eejai42/med-reminder/CarrierBox/box_v7_no_lid.stl

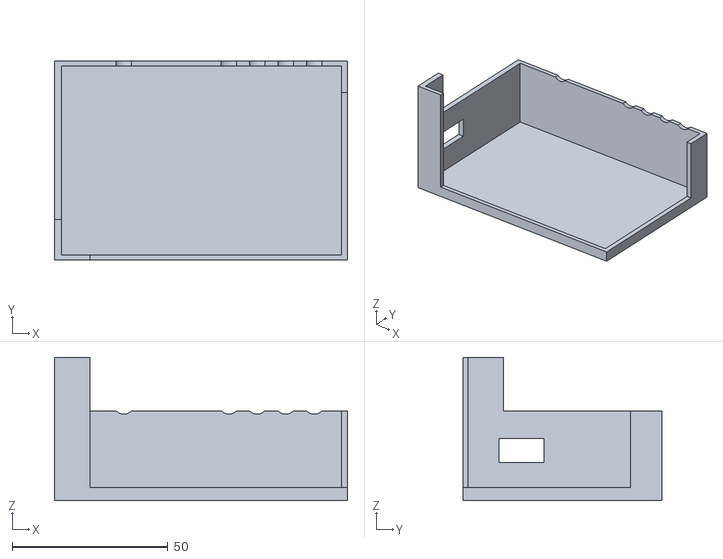
[picture p19: CAD file, 2024-03-23, an earlier design]
CarrierBox/box_v7_no_lid.stl
94.0 x 64.0 x 46.0
