eejai42/med-reminder/PillBoxInserts/InsertTestSlice_v2_1pc.stl

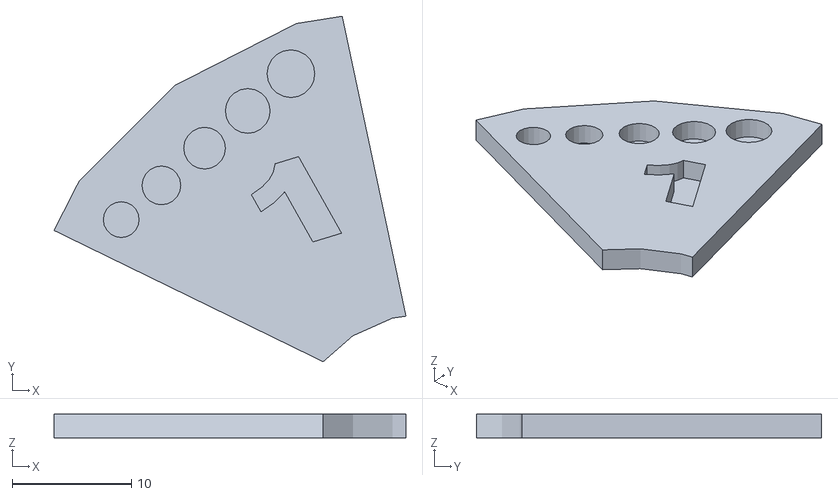
[picture p20: CAD file, 2024-03-27, an earlier design]
PillBoxInserts/InsertTestSlice_v2_1pc.stl
29.6 x 29.0 x 2.00
