eejai42/med-reminder/arduino2/Alerting.cpp

#pragma once
#include "MedReminderStateMachine.h"

bool MedReminderStateMachine::hasAlerting_MovementDetected() {
  return true;
}

void MedReminderStateMachine::enterAlerting(State currentState) {
  Serial.println("Alerting");
  delay(25 * millisPerSecond);
}
